antmicro/dual-gmsl-serializer-adapter/assets/previews/layer1.png

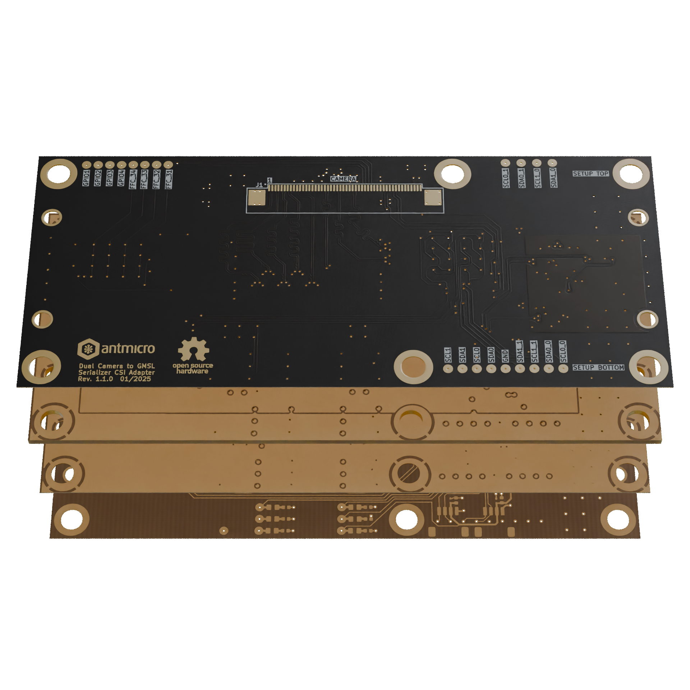
assets/previews/layer1.png
