antmicro/dual-gmsl-serializer-adapter/assets/previews/layer2.png

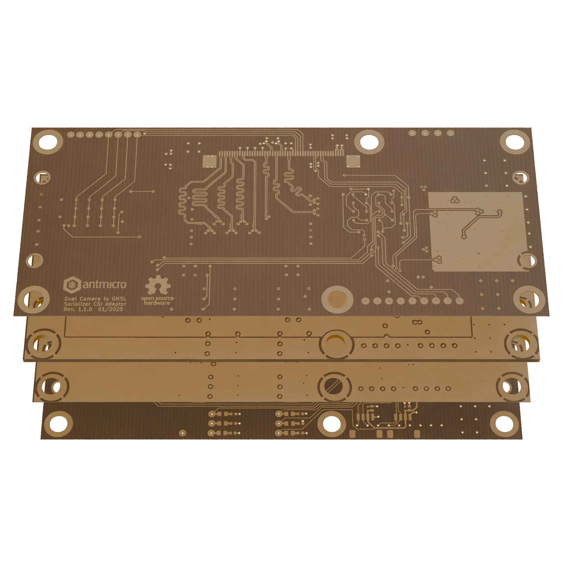
assets/previews/layer2.png
