antmicro/dual-gmsl-serializer-adapter/assets/previews/layer3.png

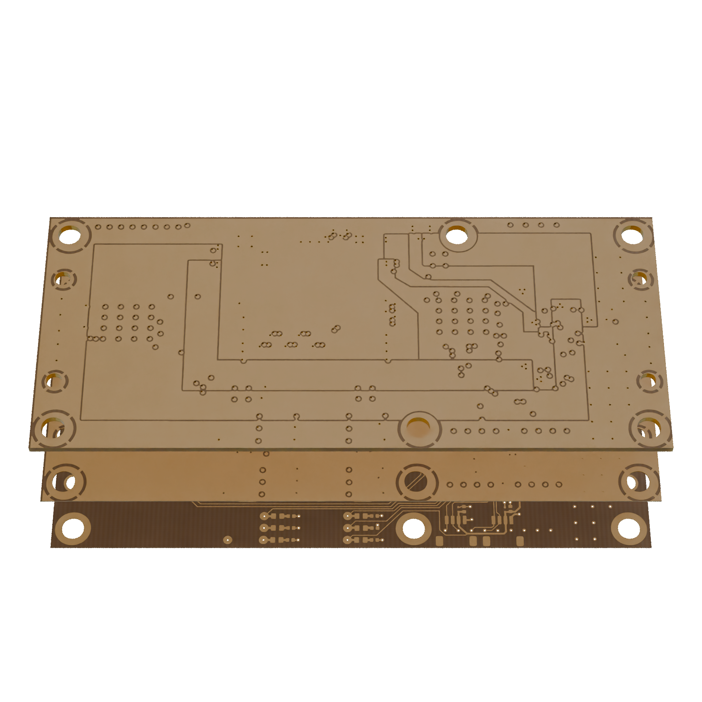
assets/previews/layer3.png
