antmicro/dual-gmsl-serializer-adapter/assets/previews/layer4.png

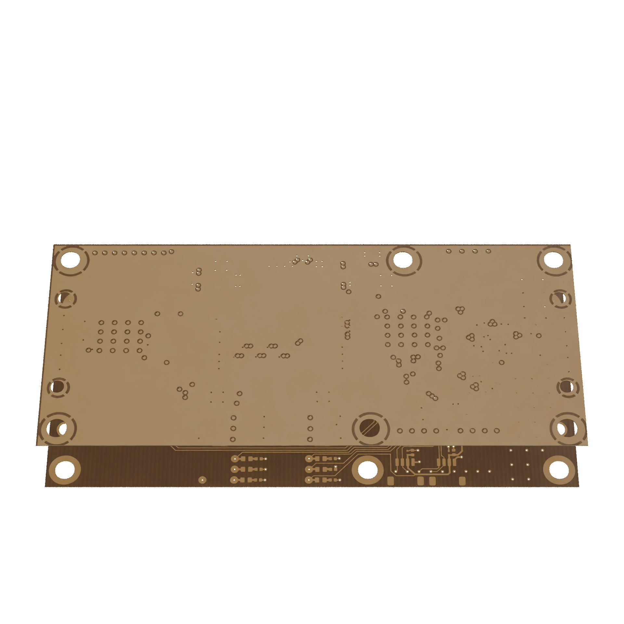
assets/previews/layer4.png
