antmicro/dual-gmsl-serializer-adapter/assets/previews/layer5.png

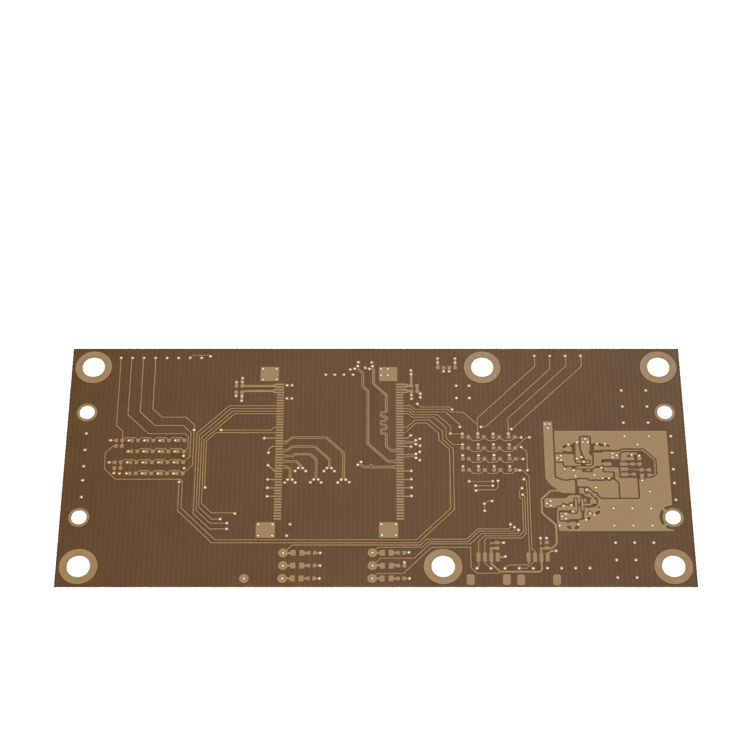
assets/previews/layer5.png
