antmicro/dual-gmsl-serializer-adapter/assets/previews/leftB.png

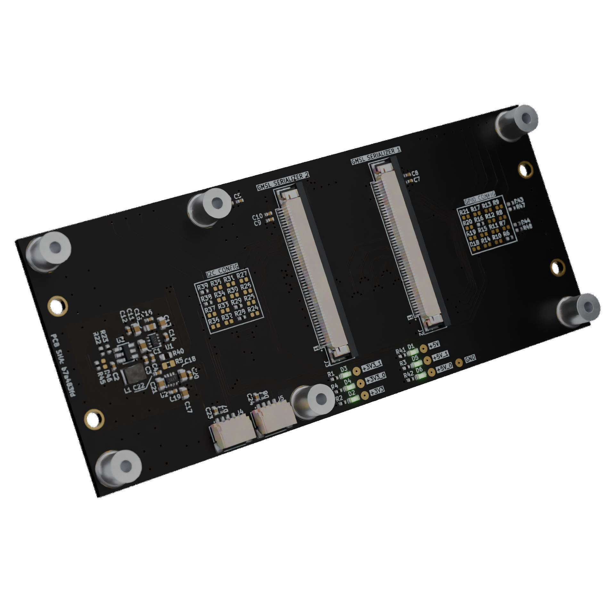
assets/previews/leftB.png
