antmicro/dual-gmsl-serializer-adapter/assets/previews/leftT.png

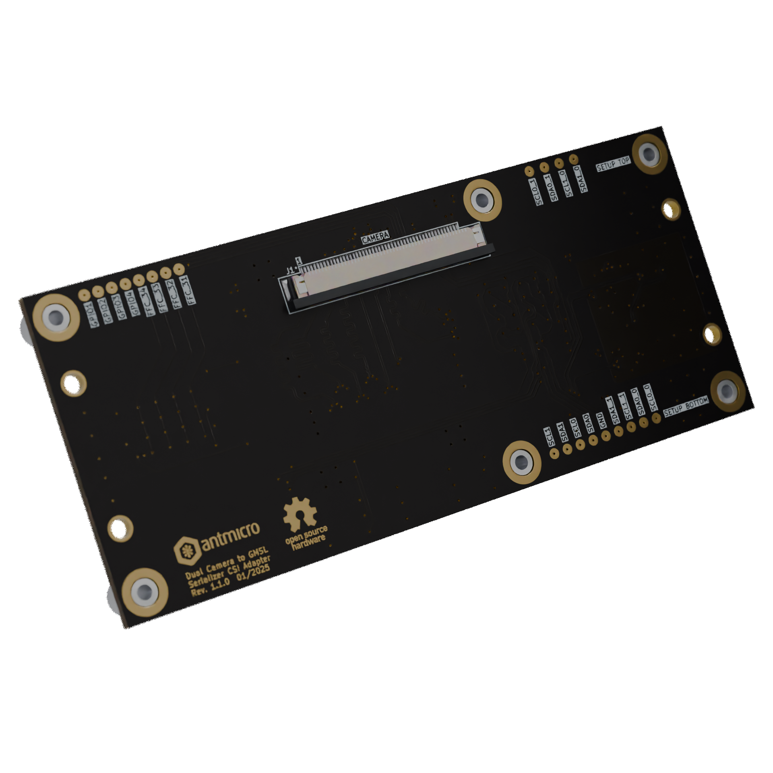
assets/previews/leftT.png
