antmicro/dual-gmsl-serializer-adapter/assets/previews/orthoB.png

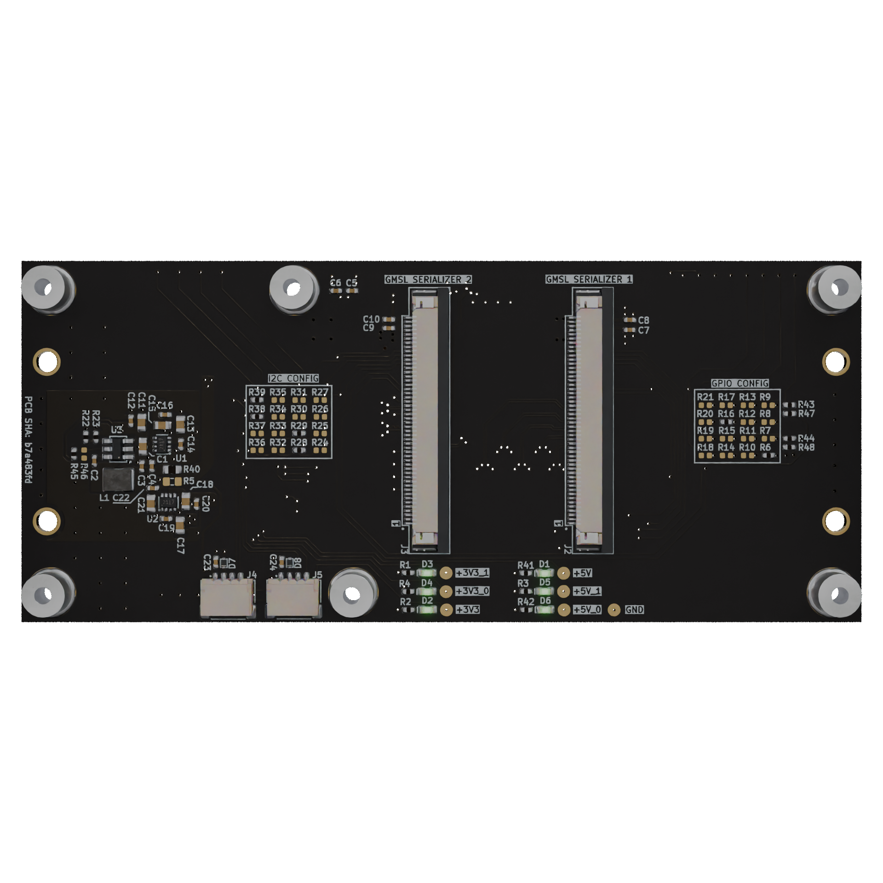
assets/previews/orthoB.png
