antmicro/dual-gmsl-serializer-adapter/assets/previews/orthoT.png

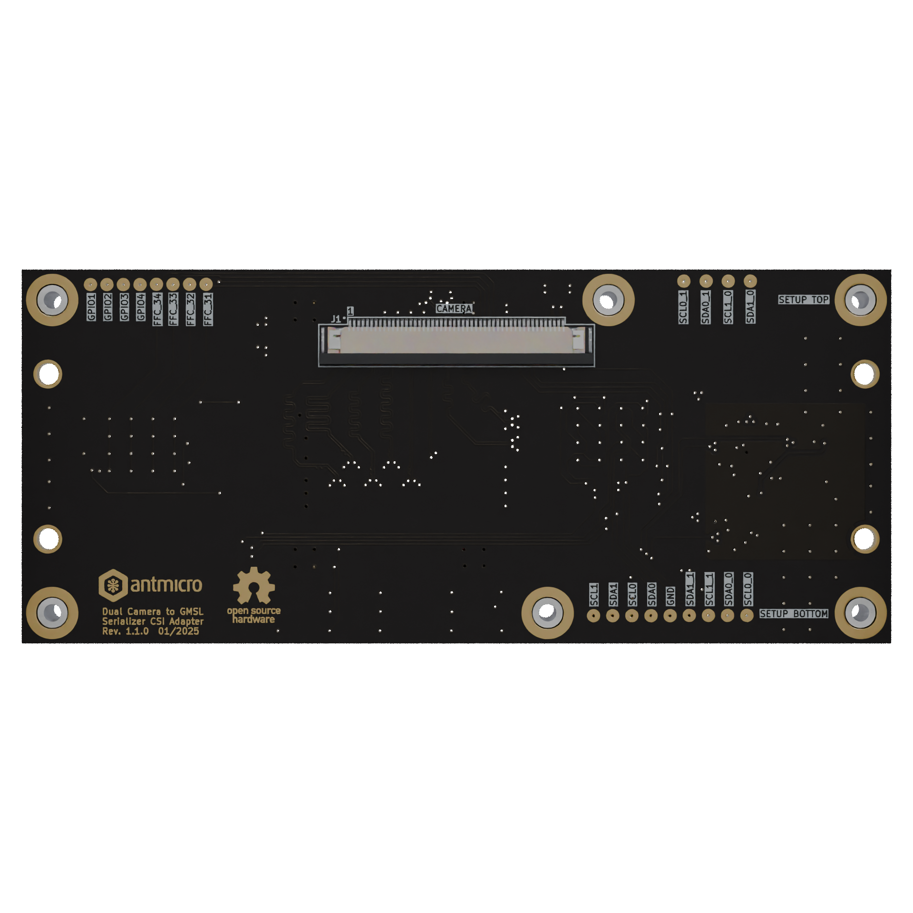
assets/previews/orthoT.png
