antmicro/dual-gmsl-serializer-adapter/assets/previews/rightB.png

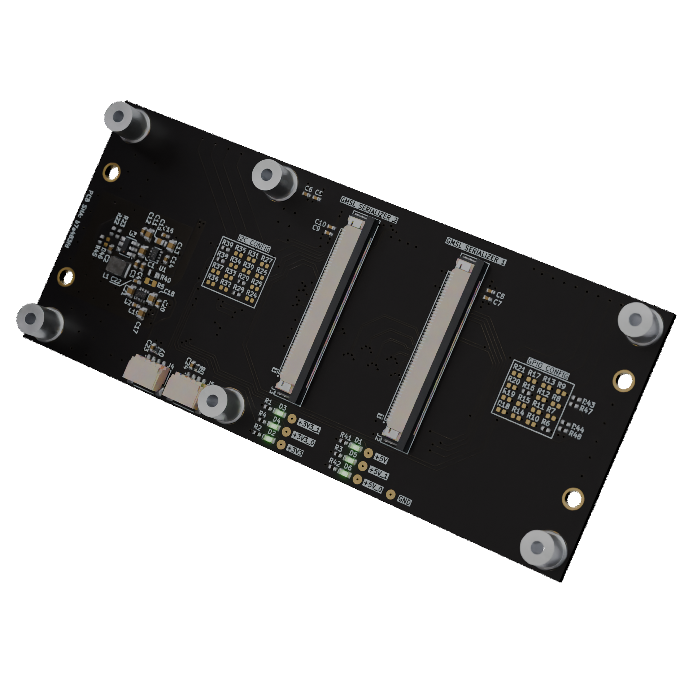
assets/previews/rightB.png
