antmicro/dual-gmsl-serializer-adapter/assets/previews/rightT.png

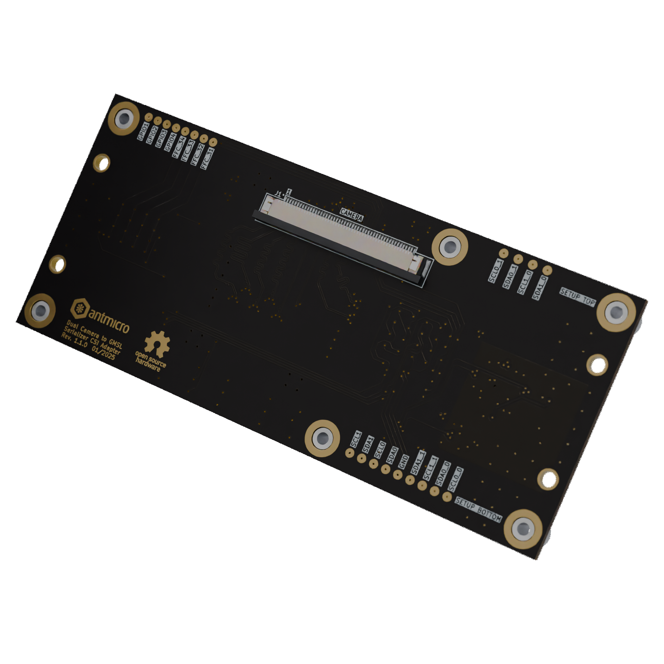
assets/previews/rightT.png
