antmicro/dual-gmsl-serializer-adapter/assets/wireframe/wireframe_descriptions_bottom.png

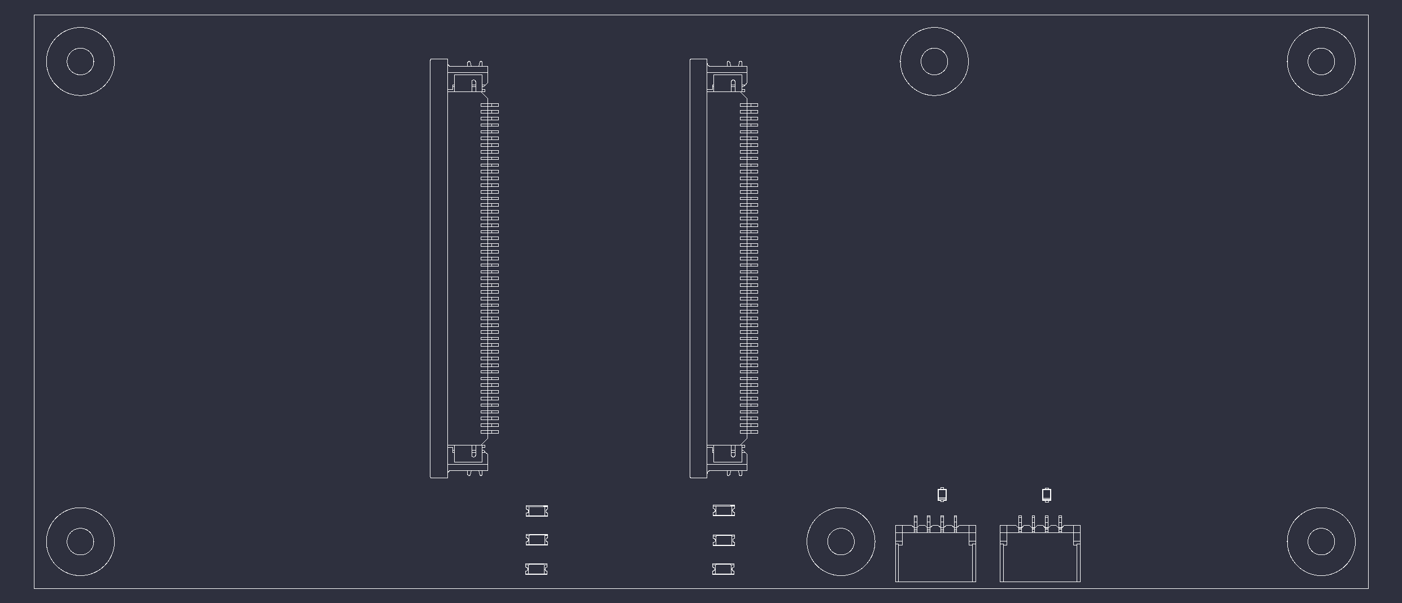
assets/wireframe/wireframe_descriptions_bottom.png
