antmicro/dual-gmsl-serializer-adapter/assets/wireframe/wireframe_descriptions_top.png

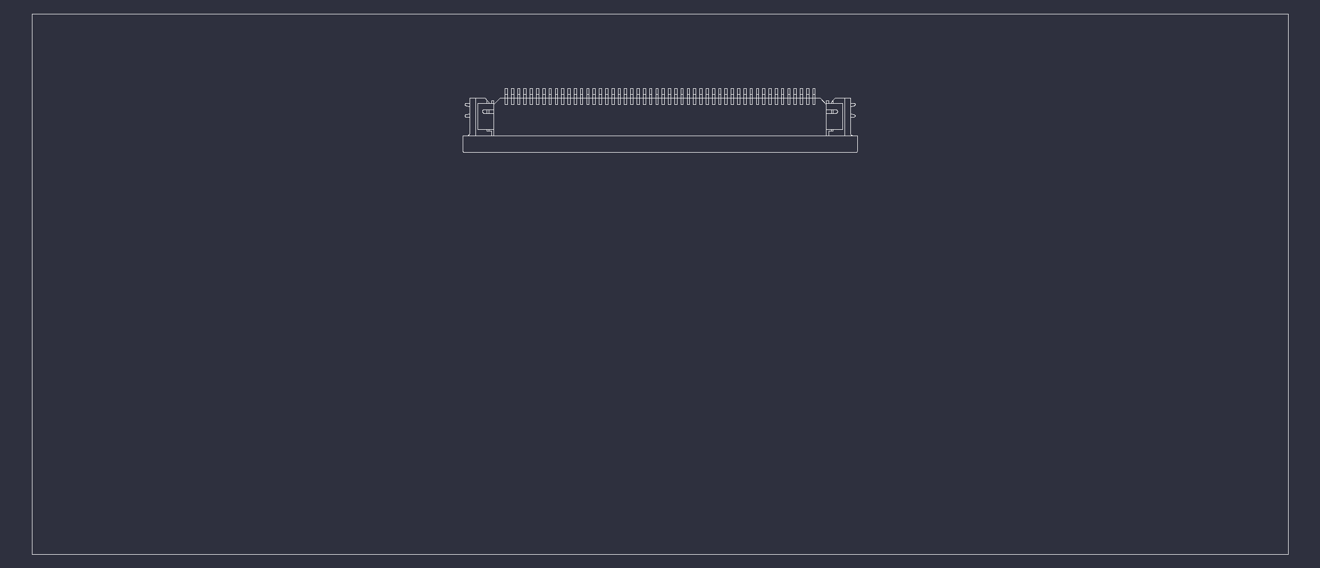
assets/wireframe/wireframe_descriptions_top.png
