antmicro/dual-gmsl-serializer-adapter/assets/wireframe/wireframe_dimensions_top.png

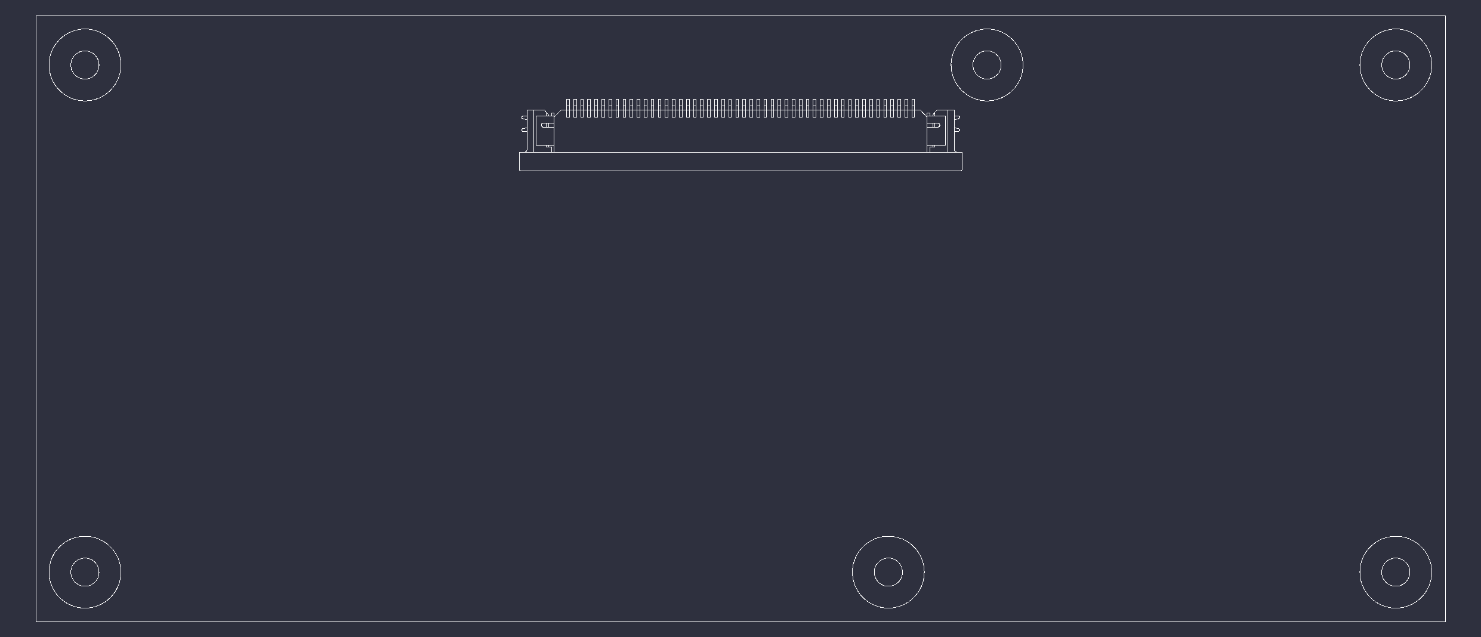
assets/wireframe/wireframe_dimensions_top.png
